gbellack/OmniView/face_software/fourFaces3.jpg

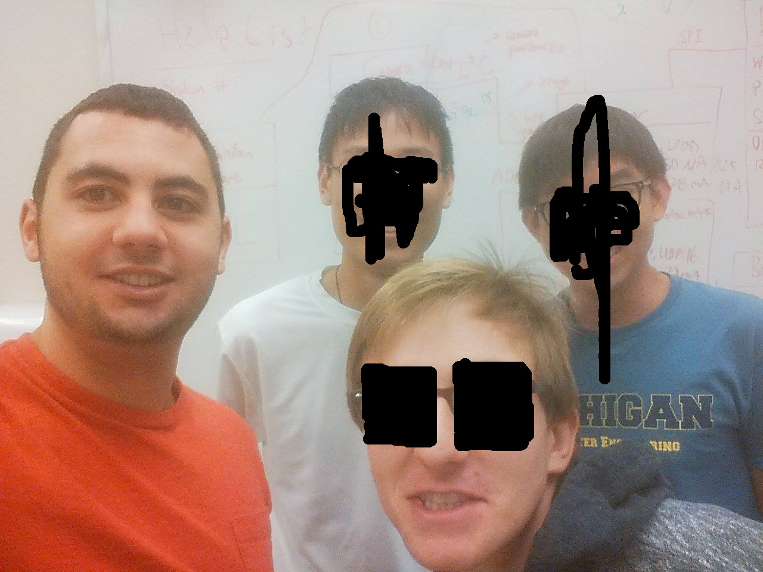
face_software/fourFaces3.jpg
