gbellack/OmniView/face_software/fourFaces.png

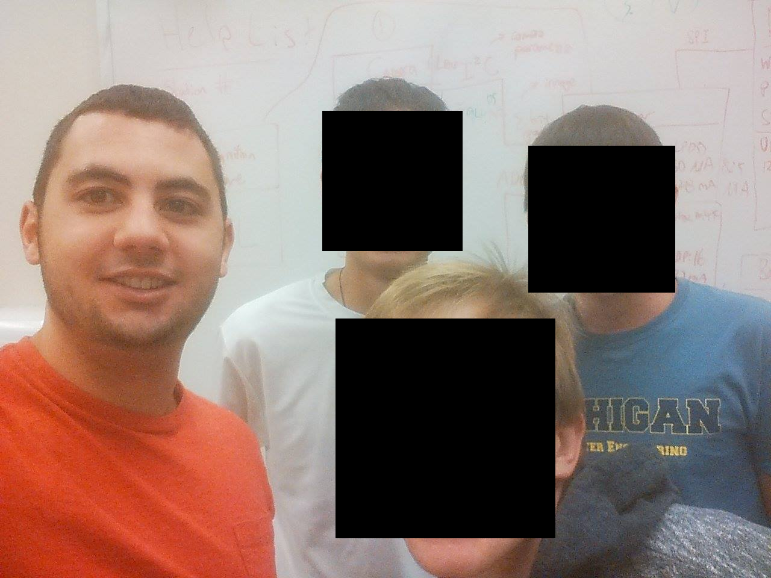
face_software/fourFaces.png
