gbellack/OmniView/face_software/training/Bobby Tan/bobby1.jpg

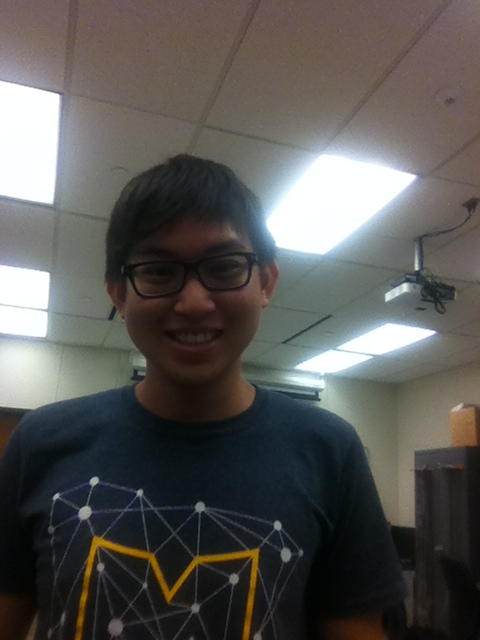
face_software/training/Bobby Tan/bobby1.jpg
