gbellack/OmniView/face_software/training/Bobby Tan/bobby2.jpg

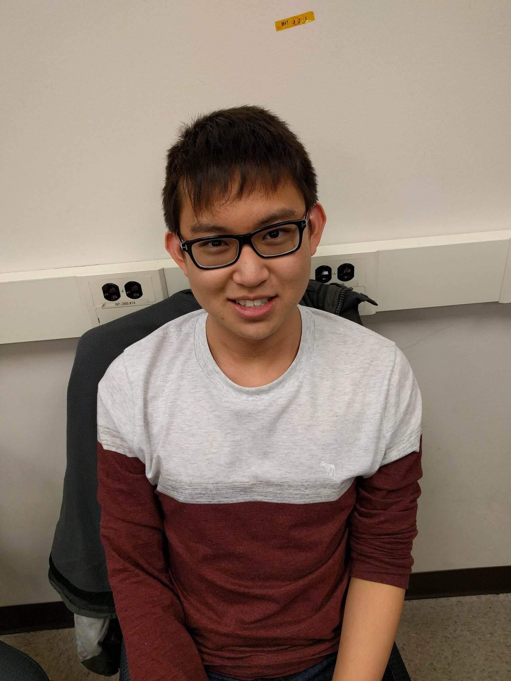
face_software/training/Bobby Tan/bobby2.jpg
