gbellack/OmniView/face_software/training/Bobby Tan/bobby3.jpg

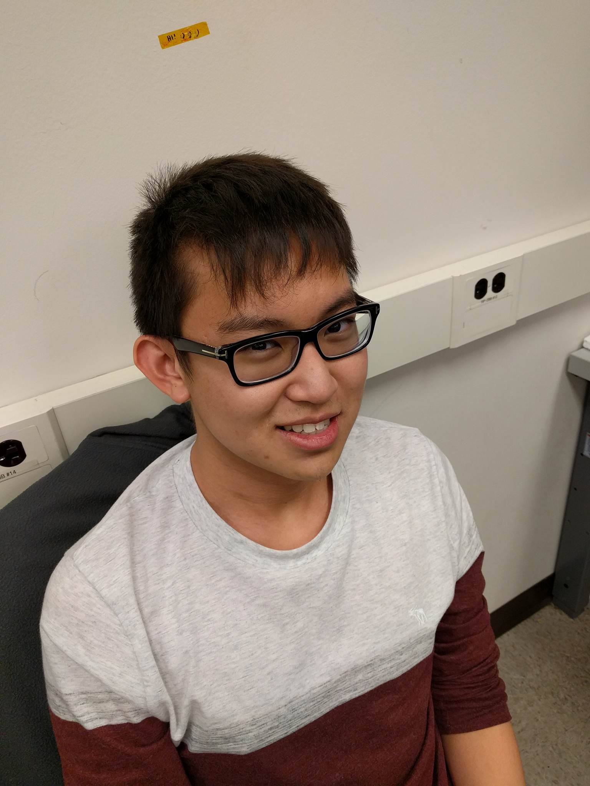
face_software/training/Bobby Tan/bobby3.jpg
