gbellack/OmniView/face_software/training/Bobby Tan/bobby4.jpg

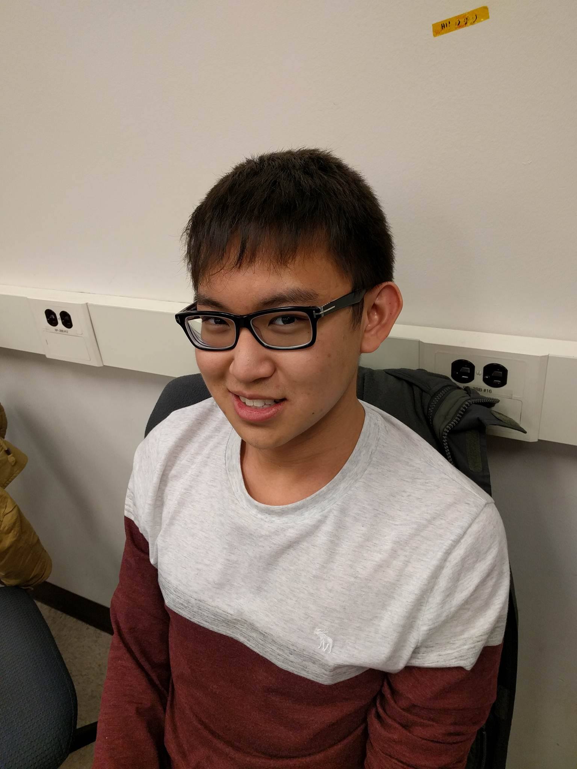
face_software/training/Bobby Tan/bobby4.jpg
