gbellack/OmniView/face_software/training/Bobby Tan/IMG_0640.JPG

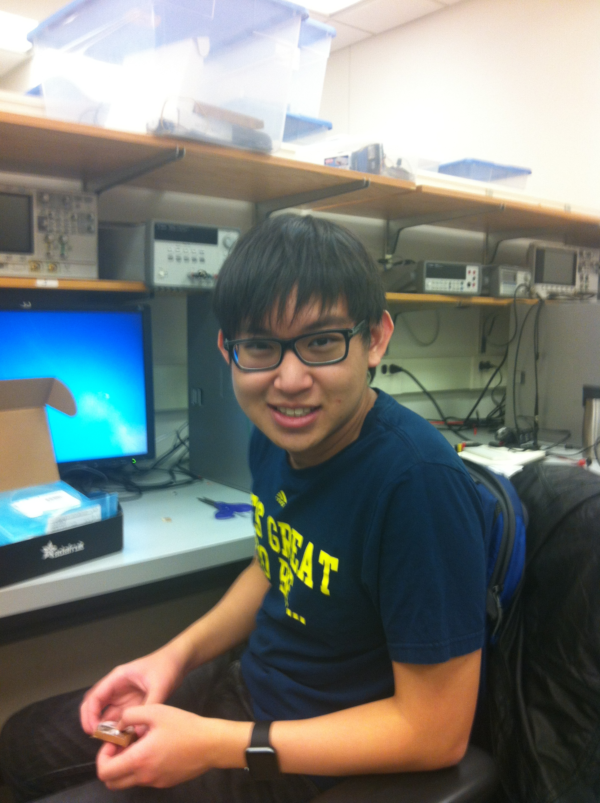
face_software/training/Bobby Tan/IMG_0640.JPG
