gbellack/OmniView/face_software/training/Garrison Bellack/garrison1.jpg

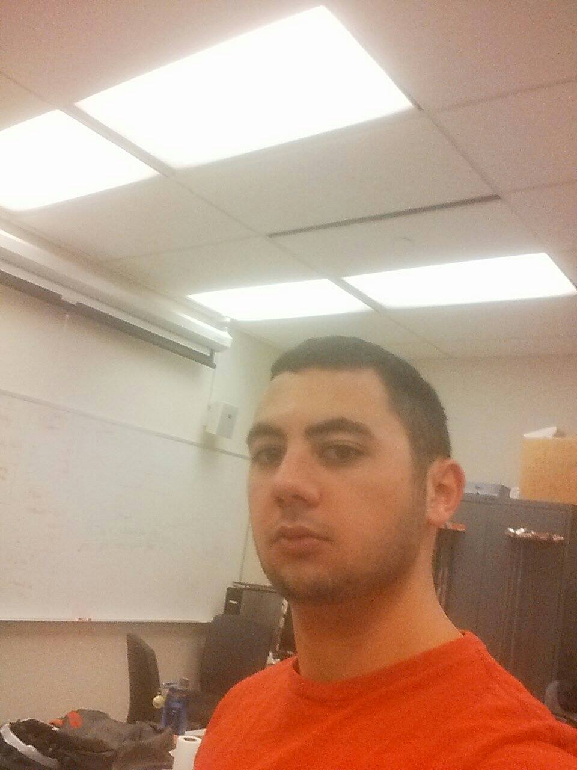
face_software/training/Garrison Bellack/garrison1.jpg
