gbellack/OmniView/face_software/training/Garrison Bellack/garrison2.jpg

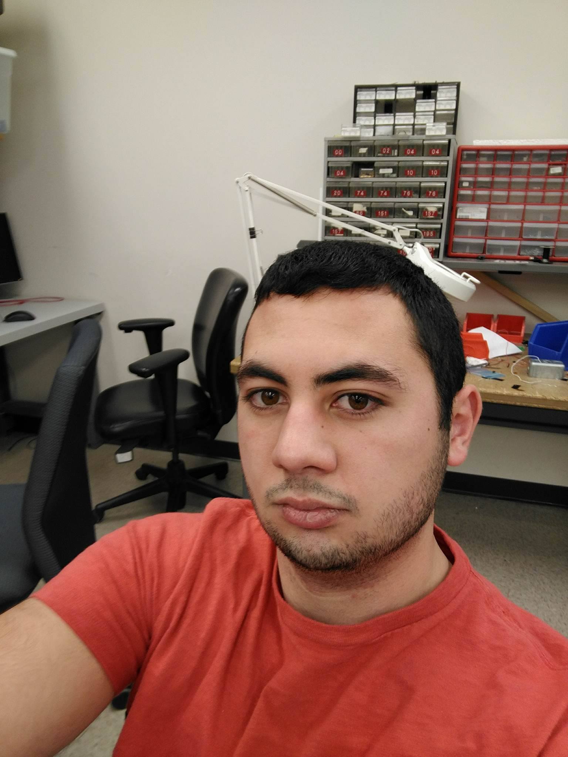
face_software/training/Garrison Bellack/garrison2.jpg
