gbellack/OmniView/face_software/training/Garrison Bellack/garrison3.jpg

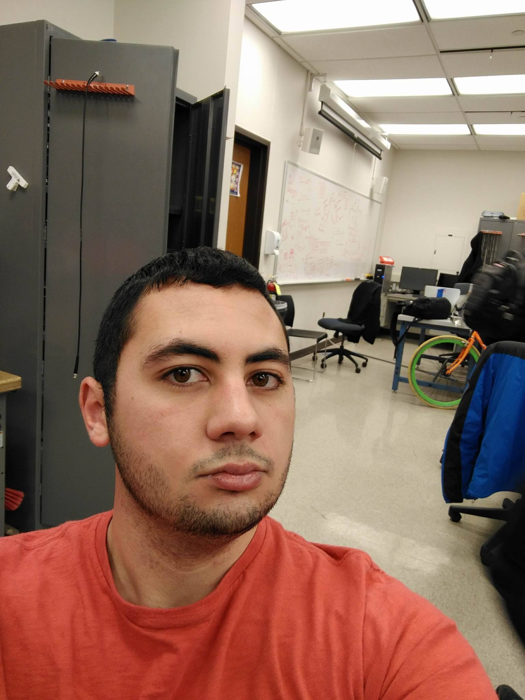
face_software/training/Garrison Bellack/garrison3.jpg
