gbellack/OmniView/face_software/training/John Connally/IMG_0642.JPG

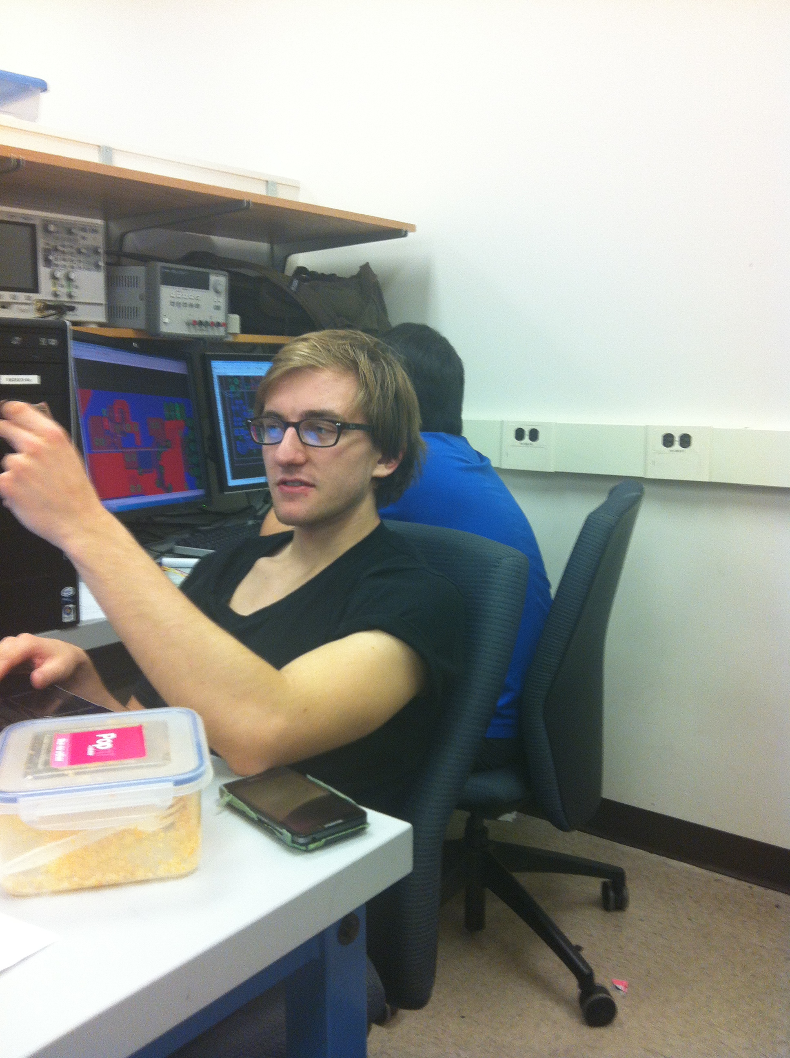
face_software/training/John Connally/IMG_0642.JPG
