gbellack/OmniView/face_software/training/John Connally/john0.jpg

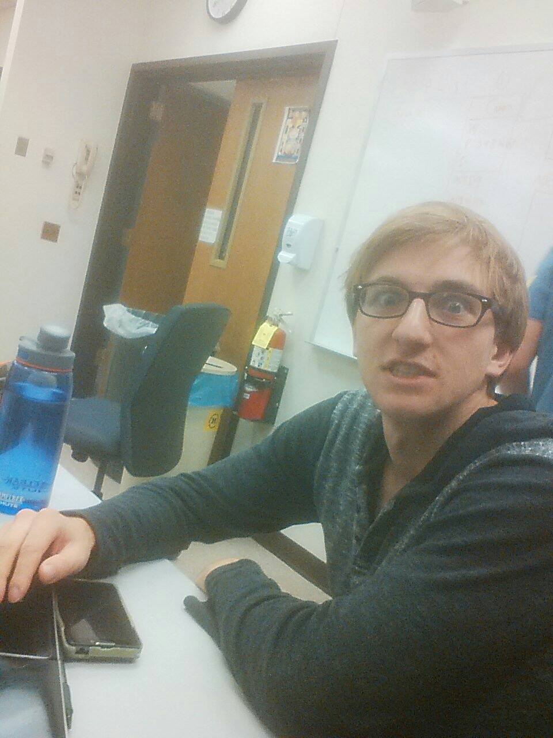
face_software/training/John Connally/john0.jpg
