gbellack/OmniView/face_software/training/John Connally/john1.jpg

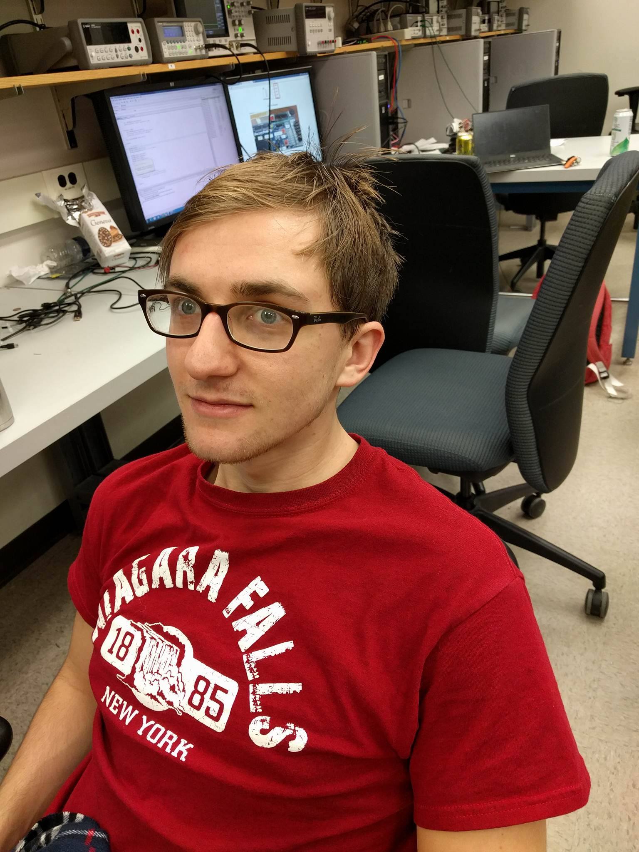
face_software/training/John Connally/john1.jpg
