gbellack/OmniView/face_software/training/John Connally/john3.jpg

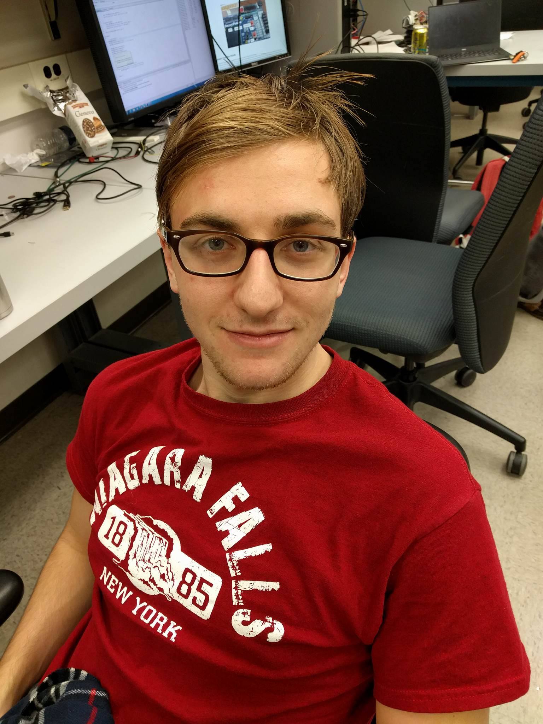
face_software/training/John Connally/john3.jpg
