gbellack/OmniView/face_software/training/Loren Wang/IMG_0644.JPG

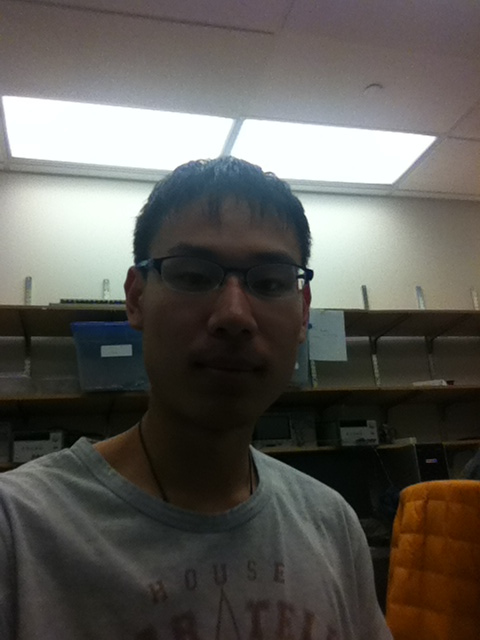
face_software/training/Loren Wang/IMG_0644.JPG
