gbellack/OmniView/face_software/training/Loren Wang/loren1.jpg

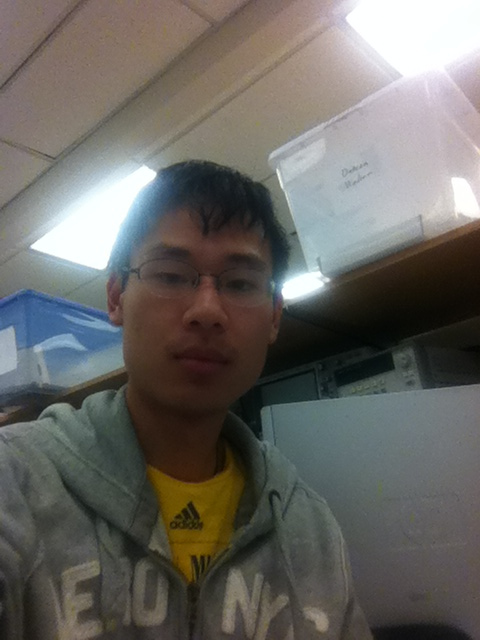
face_software/training/Loren Wang/loren1.jpg
