gbellack/OmniView/face_software/training/Loren Wang/loren2.jpg

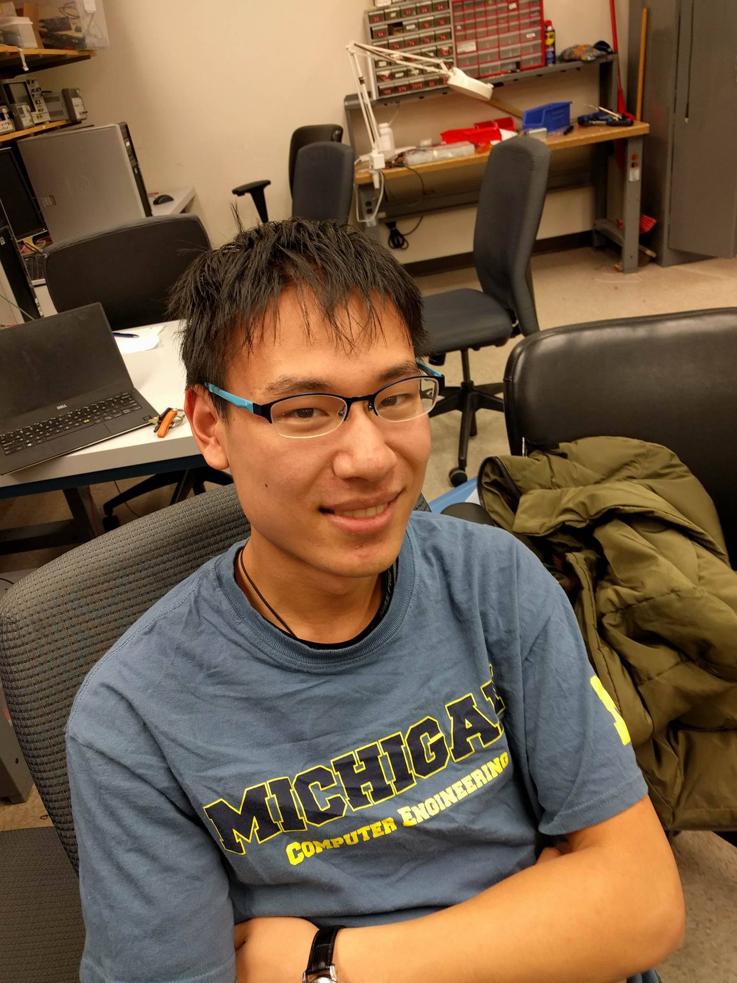
face_software/training/Loren Wang/loren2.jpg
