gbellack/OmniView/face_software/training/Loren Wang/loren3.jpg

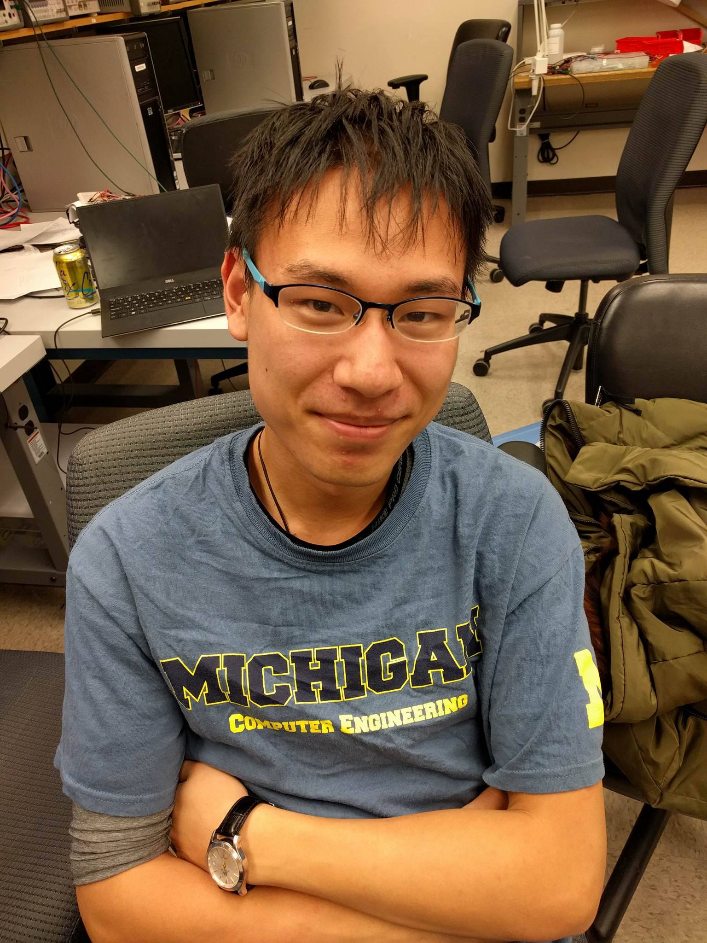
face_software/training/Loren Wang/loren3.jpg
