gbellack/OmniView/face_software/training/Loren Wang/loren4.jpg

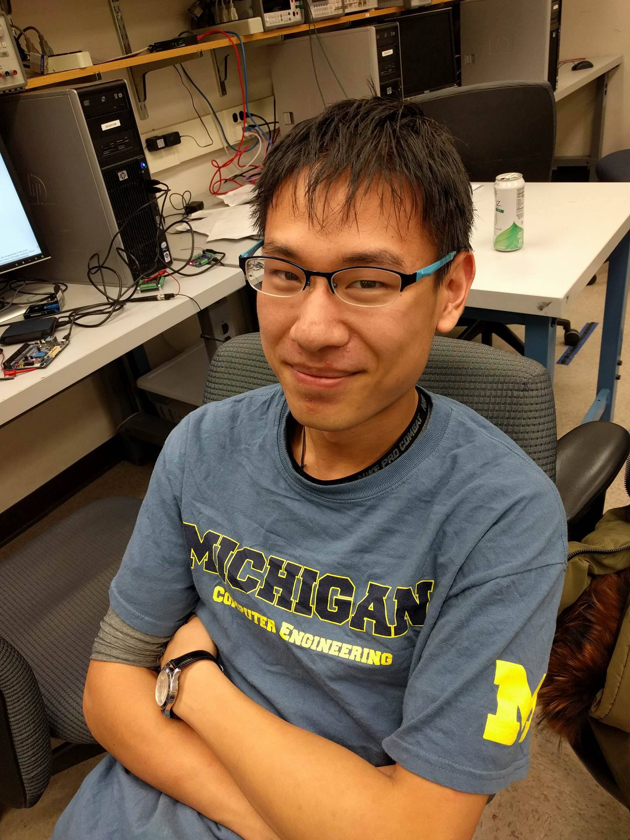
face_software/training/Loren Wang/loren4.jpg
