gbellack/OmniView/face_software/training/Mark Brehob/IMG_0657.JPG

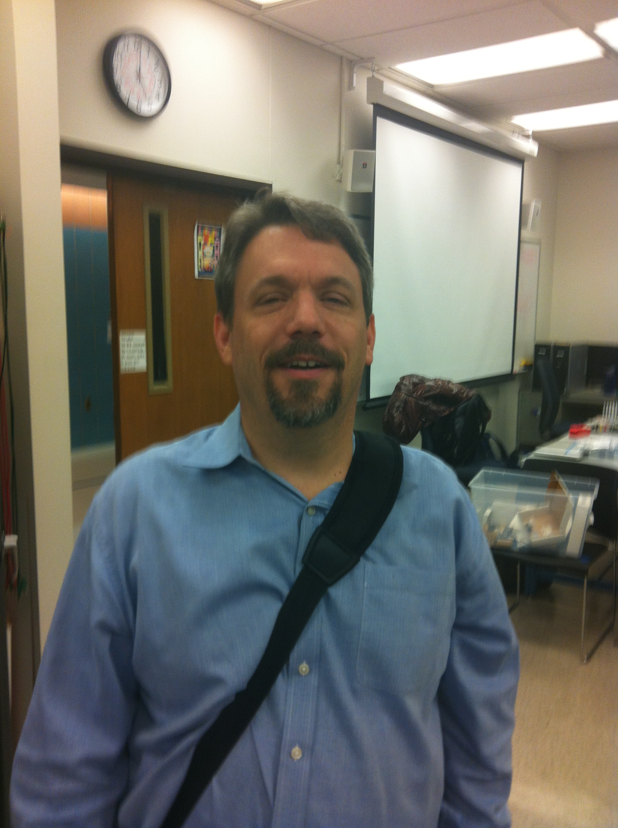
face_software/training/Mark Brehob/IMG_0657.JPG
