gbellack/OmniView/face_software/training/Mark Brehob/IMG_0658.JPG

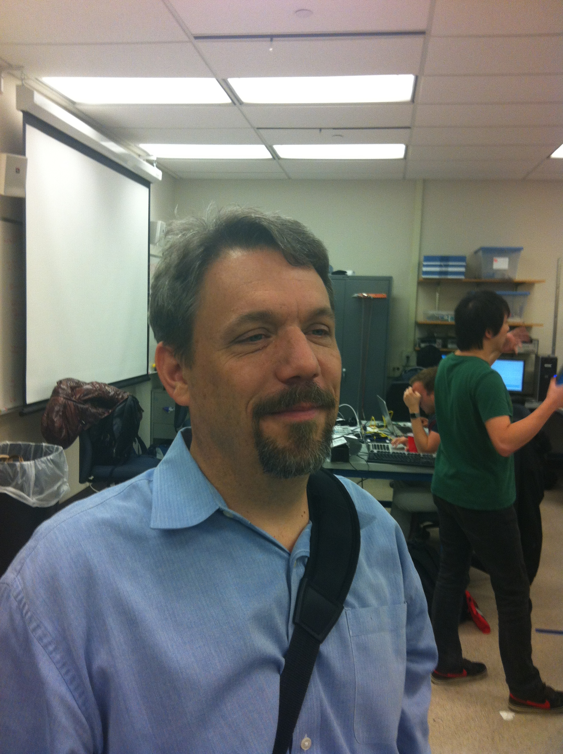
face_software/training/Mark Brehob/IMG_0658.JPG
