gbellack/OmniView/face_software/training/Mark Brehob/IMG_0659.JPG

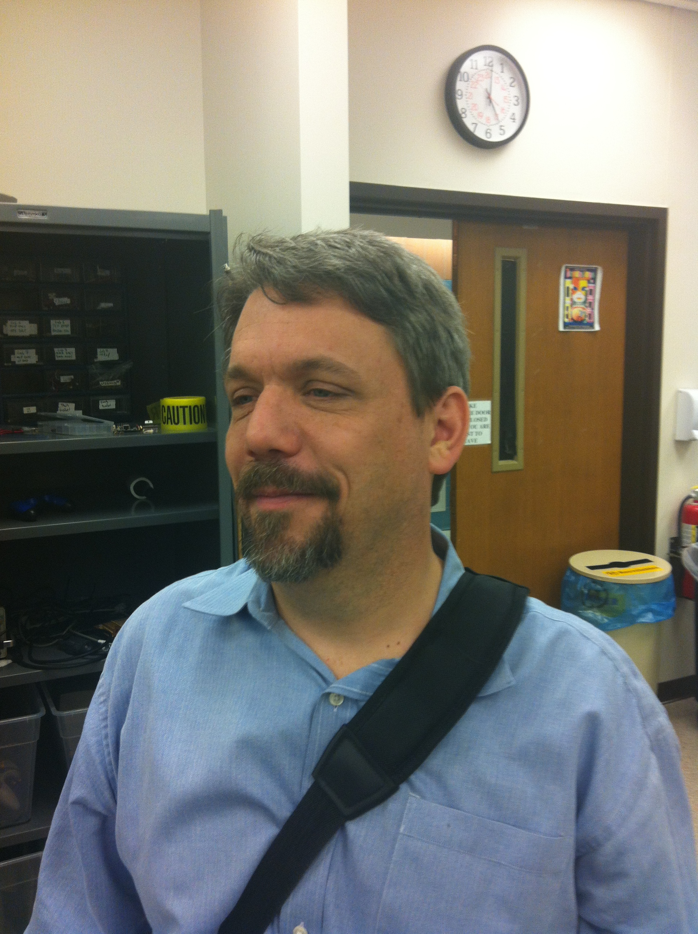
face_software/training/Mark Brehob/IMG_0659.JPG
