gbellack/OmniView/face_software/training/Matthew Smith/IMG_0661.JPG

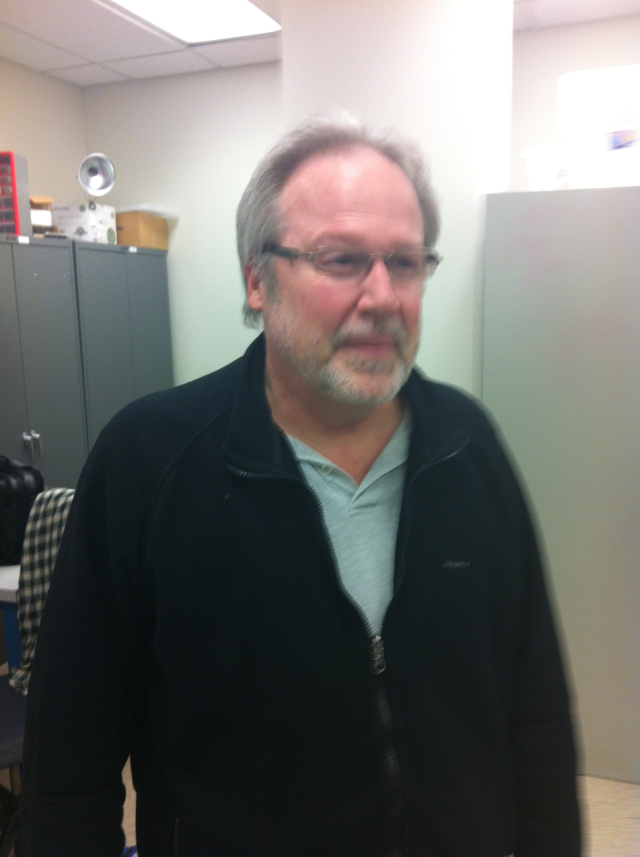
face_software/training/Matthew Smith/IMG_0661.JPG
