gbellack/OmniView/face_software/training/Matthew Smith/IMG_0662.JPG

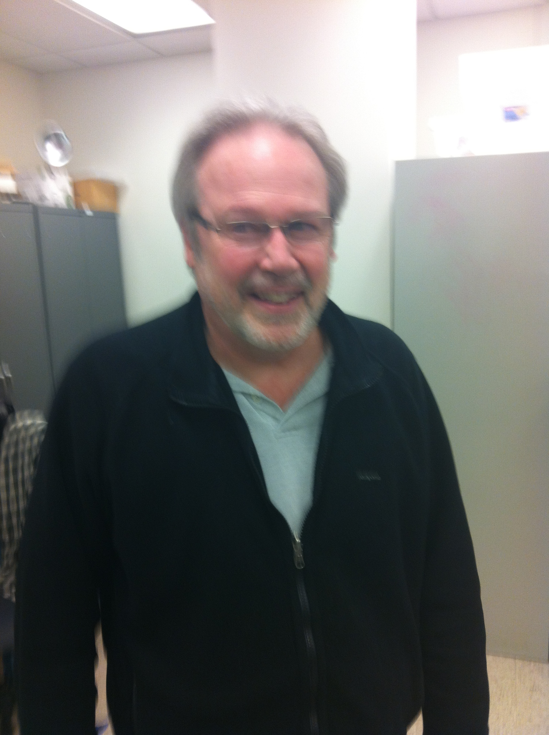
face_software/training/Matthew Smith/IMG_0662.JPG
