gbellack/OmniView/face_software/training/Tzu-Fei Yu/tzu0.jpg

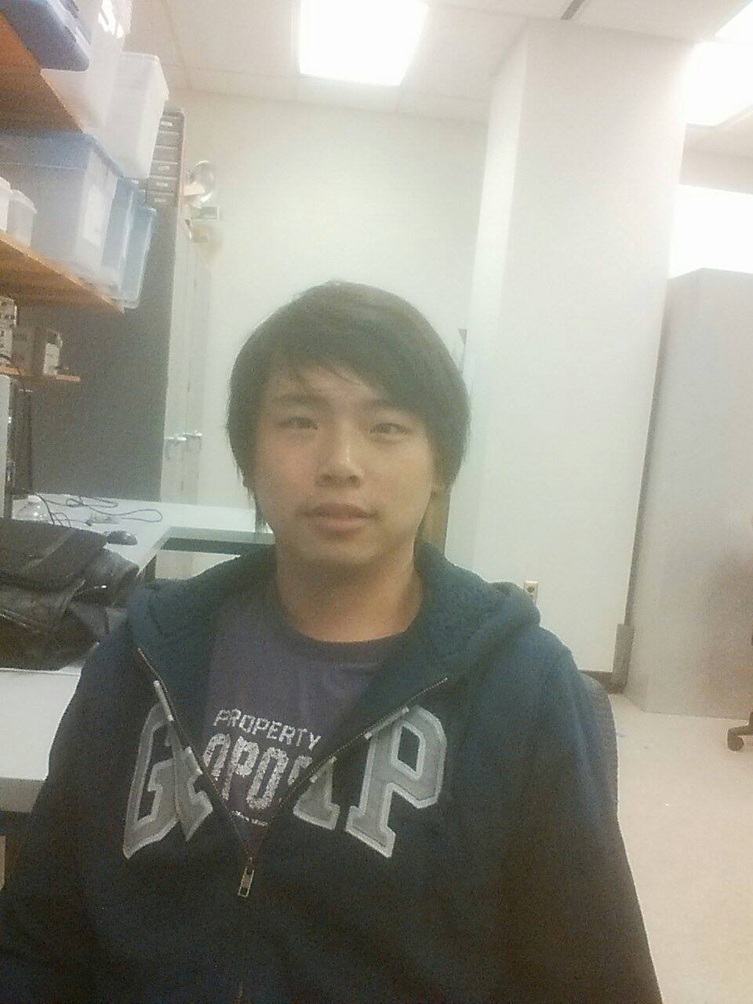
face_software/training/Tzu-Fei Yu/tzu0.jpg
