gbellack/OmniView/face_software/training/Tzu-Fei Yu/tzu1.jpg

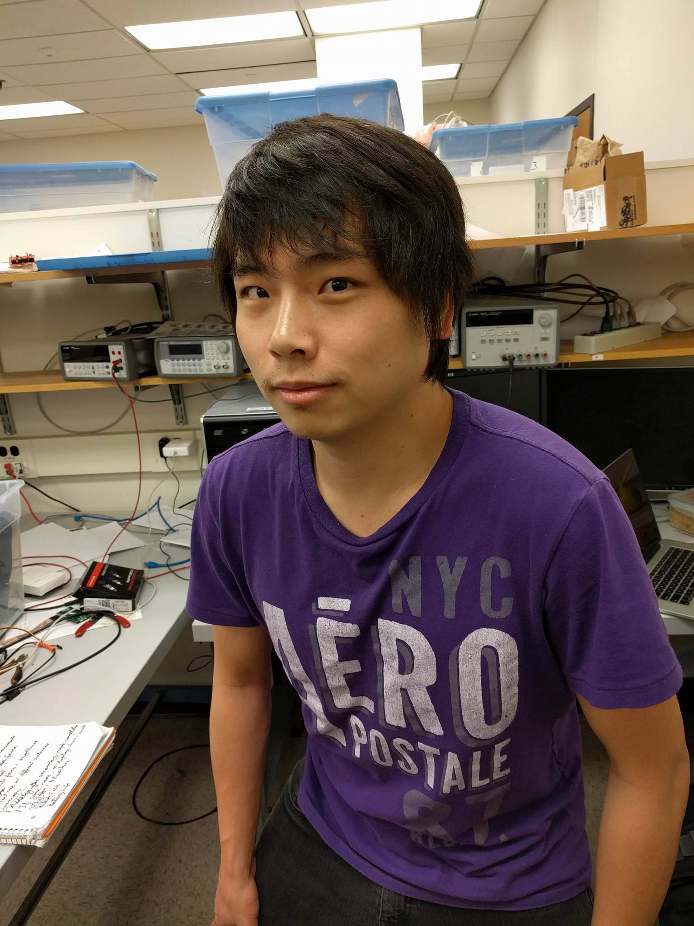
face_software/training/Tzu-Fei Yu/tzu1.jpg
