gbellack/OmniView/face_software/training/Tzu-Fei Yu/tzu2.JPG

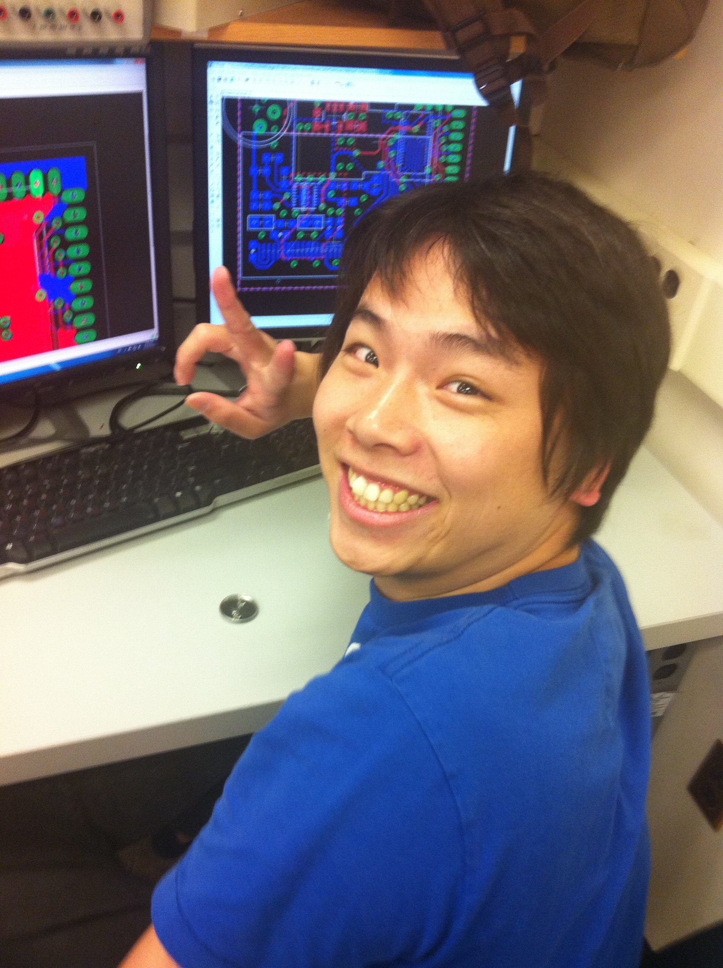
face_software/training/Tzu-Fei Yu/tzu2.JPG
