gbellack/OmniView/face_software/training/Tzu-Fei Yu/tzu3.jpg

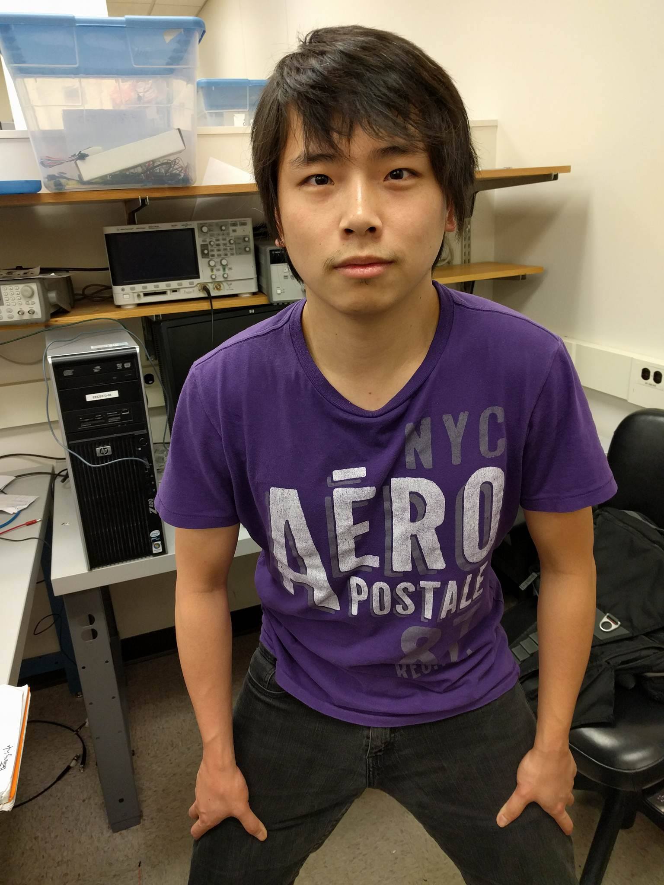
face_software/training/Tzu-Fei Yu/tzu3.jpg
