gbellack/OmniView/face_software/training/Tzu-Fei Yu/tzu4.jpg

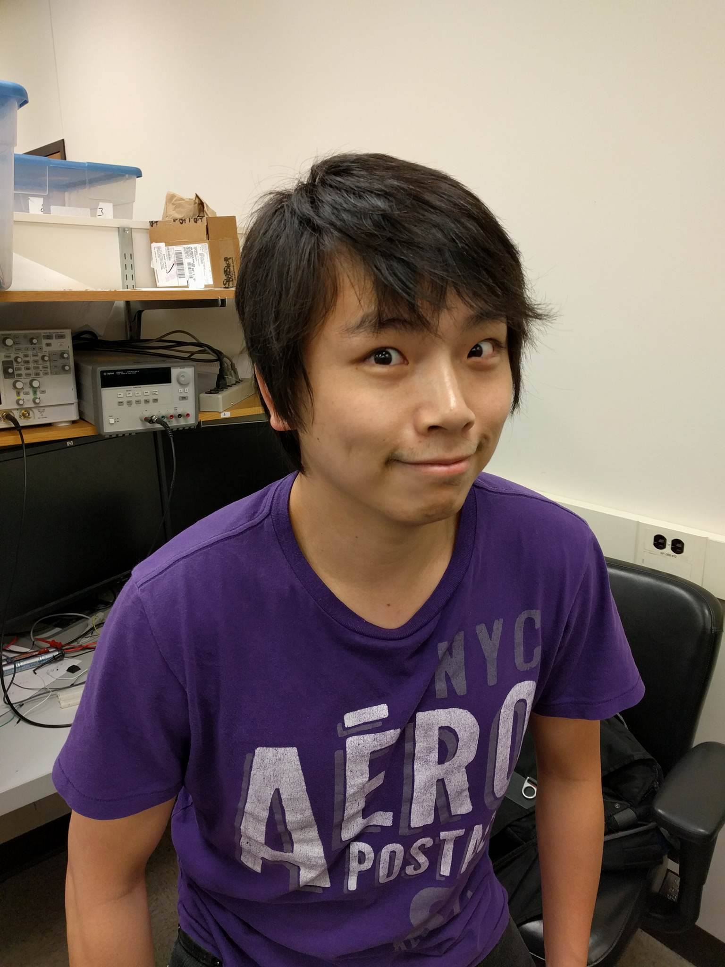
face_software/training/Tzu-Fei Yu/tzu4.jpg
