gbellack/OmniView/face_software/training/Yitian Chen/IMG_0663.JPG

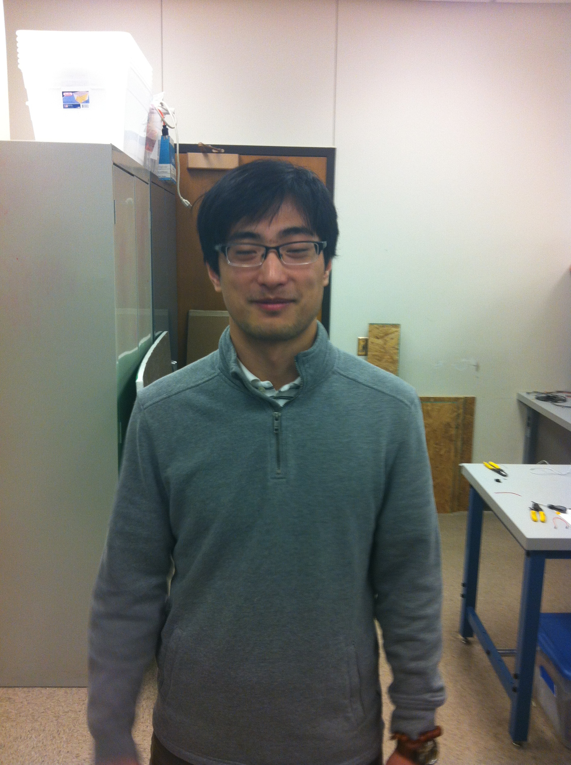
face_software/training/Yitian Chen/IMG_0663.JPG
