gbellack/OmniView/face_software/training/Yitian Chen/IMG_0664.JPG

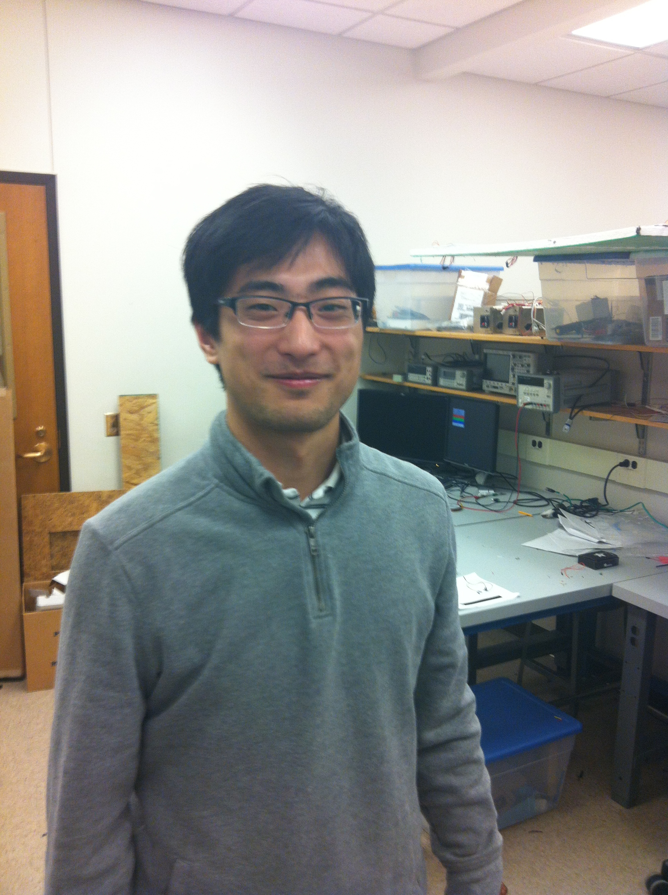
face_software/training/Yitian Chen/IMG_0664.JPG
