gbellack/OmniView/datasheets/Adafruit/displayDriver/display_driver.h

#ifndef DISPLAY_DRIVER_H
#define DISPLAY_DRIVER_H

#include "Arduino.h"

#include <Wire.h>
#include <SPI.h>

#define BLACK 0
#define WHITE 1
#define INVERSE 2

#define SSD1306_I2C_ADDRESS   0x3C

#define SSD1306_128_64

#define SSD1306_LCDWIDTH                  128
#define SSD1306_LCDHEIGHT                 64

#define SSD1306_SETCONTRAST 0x81
#define SSD1306_DISPLAYALLON_RESUME 0xA4
#define SSD1306_DISPLAYALLON 0xA5
#define SSD1306_NORMALDISPLAY 0xA6
#define SSD1306_INVERTDISPLAY 0xA7
#define SSD1306_DISPLAYOFF 0xAE
#define SSD1306_DISPLAYON 0xAF

#define SSD1306_SETDISPLAYOFFSET 0xD3
#define SSD1306_SETCOMPINS 0xDA

#define SSD1306_SETVCOMDETECT 0xDB

#define SSD1306_SETDISPLAYCLOCKDIV 0xD5
#define SSD1306_SETPRECHARGE 0xD9

#define SSD1306_SETMULTIPLEX 0xA8

#define SSD1306_SETLOWCOLUMN 0x00
#define SSD1306_SETHIGHCOLUMN 0x10

#define SSD1306_SETSTARTLINE 0x40

#define SSD1306_MEMORYMODE 0x20
#define SSD1306_COLUMNADDR 0x21
#define SSD1306_PAGEADDR   0x22

#define SSD1306_COMSCANINC 0xC0
#define SSD1306_COMSCANDEC 0xC8

#define SSD1306_SEGREMAP 0xA0

#define SSD1306_CHARGEPUMP 0x8D

#define SSD1306_EXTERNALVCC 0x1
#define SSD1306_SWITCHCAPVCC 0x2

// Scrolling #defines
#define SSD1306_ACTIVATE_SCROLL 0x2F
#define SSD1306_DEACTIVATE_SCROLL 0x2E
#define SSD1306_SET_VERTICAL_SCROLL_AREA 0xA3
#define SSD1306_RIGHT_HORIZONTAL_SCROLL 0x26
#define SSD1306_LEFT_HORIZONTAL_SCROLL 0x27
#define SSD1306_VERTICAL_AND_RIGHT_HORIZONTAL_SCROLL 0x29
#define SSD1306_VERTICAL_AND_LEFT_HORIZONTAL_SCROLL 0x2A

#define swap(a, b) { int16_t t = a; a = b; b = t; }

/* Printing functions */
void print(const char *str);
void println(const char *str);
void printHelper(uint8_t c);

void fillRect(int16_t x, int16_t y, int16_t w, int16_t h, uint16_t color);
void drawFastVLine(int16_t x, int16_t y, int16_t h, uint16_t color);
void drawFastVLineInternal(int16_t x, int16_t __y, int16_t __h, uint16_t color);
void drawFastHLineInternal(int16_t x, int16_t y, int16_t w, uint16_t color);

// These exist only with Adafruit_GFX (no subclass overrides)
void drawChar(int16_t x, int16_t y, unsigned char c, uint16_t color, uint16_t bg, uint8_t size);
void setCursor(int16_t x, int16_t y);
void setTextColor(uint16_t c);
void setTextColor(uint16_t c, uint16_t bg);
void setTextSize(uint8_t s);
void setTextWrap(boolean w);

int16_t height();
int16_t width();

// get current cursor position (get rotation safe maximum values, using: width() for x, height() for y)
int16_t getCursorX();
int16_t getCursorY();

uint8_t getRotation();

void initGFX(int16_t w, int16_t h);

/////////////////////////////////////////////////////////////////////////////////////////////////////////////////
// SSD1306
/////////////////////////////////////////////////////////////////////////////////////////////////////////////////

void begin(uint8_t switchvcc = SSD1306_SWITCHCAPVCC, uint8_t i2caddr = SSD1306_I2C_ADDRESS, bool reset=true);
void ssd1306_command(uint8_t c);
void ssd1306_data(uint8_t c);

void clearDisplay();
void display();

void startscrollright(uint8_t start, uint8_t stop);
void startscrollleft(uint8_t start, uint8_t stop);

void stopscroll();

void dim(bool dim);

void drawPixel(int16_t x, int16_t y, uint16_t color);

#endif
