gbellack/OmniView/modules/display/display_network.h

#ifndef DISPLAY_NETWORK_H
#define DISPLAY_NETWORK_H

/* This file contains the networking interface for anything related to the display
 * Contains functions that fetches the names etc.
 */

/* EFFECTS: Fetches the names over the network and returns them. */
extern char *FetchNames();


#endif
